ZDYnb/TEC_Driver/hardware/interview.kicad_pcb

## KiCad design Schematic/LaserTag.kicad_sch

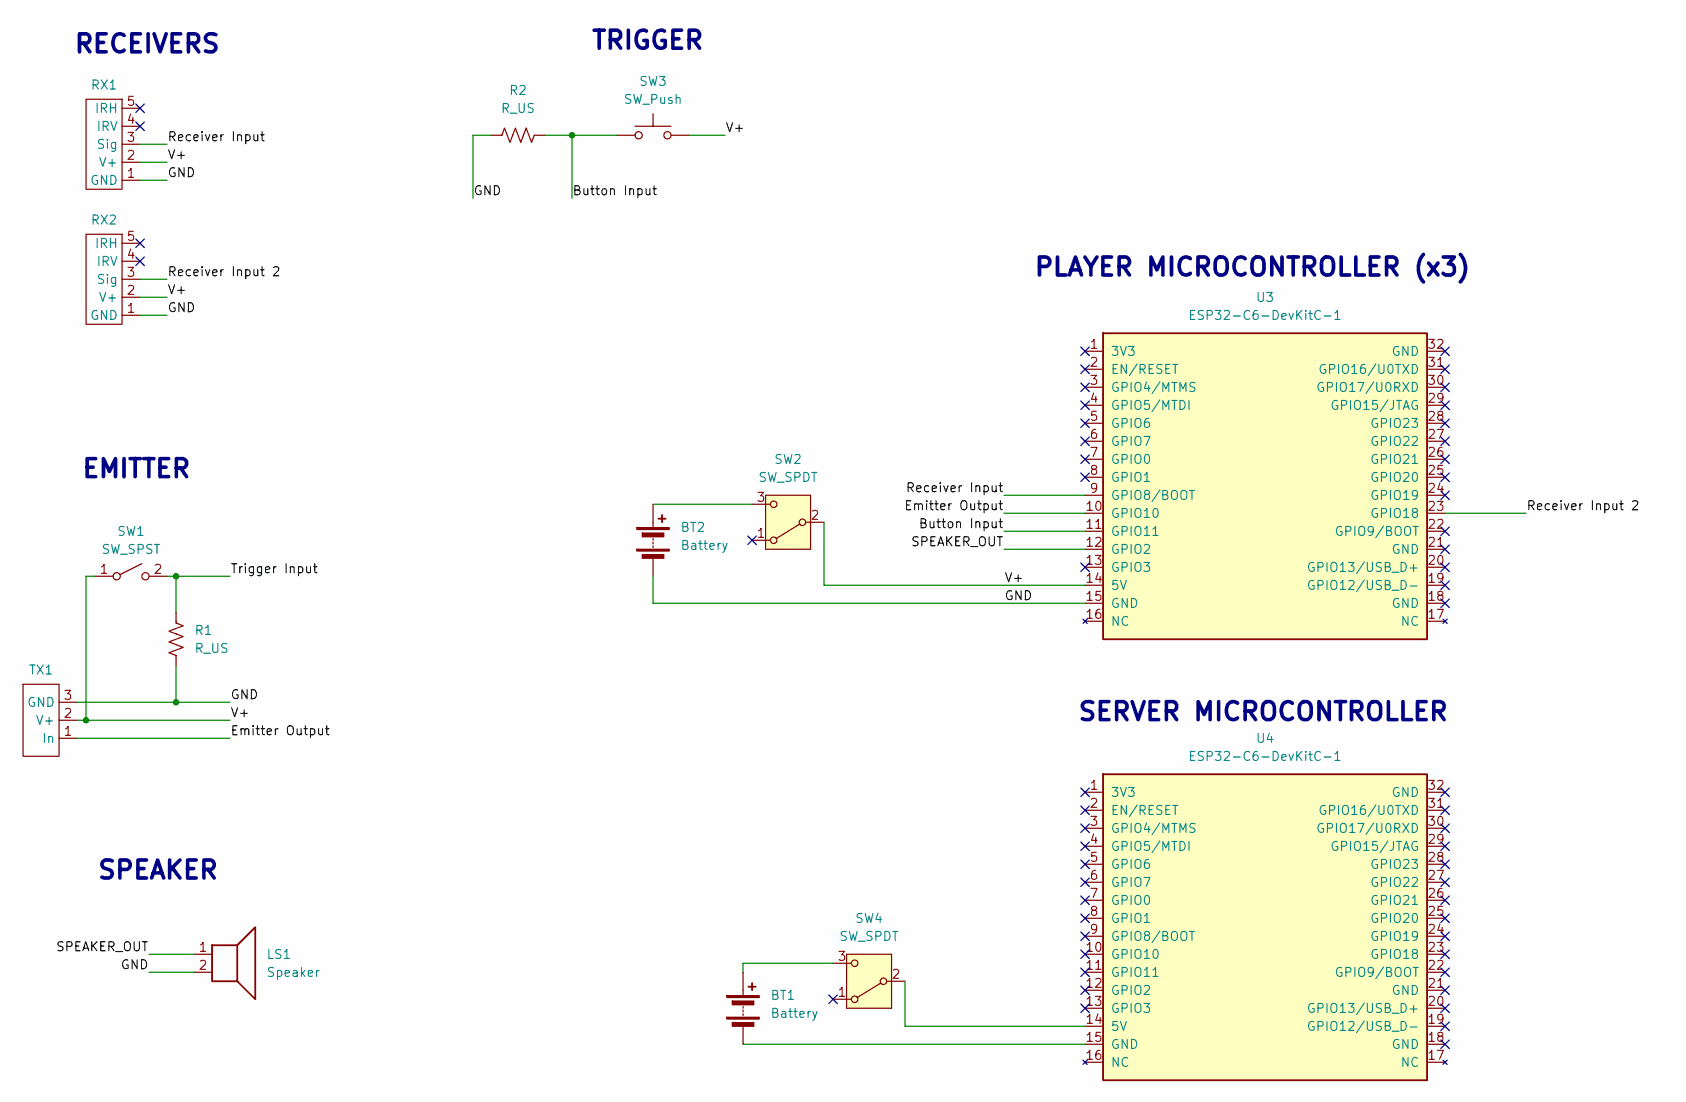
[picture p4: schematic LaserTag.kicad_sch]

Parts:
BT1, BT2: Battery
LS1: Speaker
R1, R2: R_US
RX1, RX2: (no value)
SW1: SW_SPST
SW2, SW4: SW_SPDT
SW3: SW_Push
TX1: (no value)
U3, U4: ESP32-C6-DevKitC-1

Connections:
Button Input: R2.2, SW3.1, U3.11 (GPIO11)
Emitter Output: TX1.1 (In), U3.10 (GPIO10)
GND: BT2.2 (-), LS1.2, R1.2, R2.1, RX1.1 (GND), RX2.1 (GND), TX1.3 (GND), U3.15 (GND)
unnamed: BT1.1 (+), SW4.3 (C)
unnamed: BT1.2 (-), U4.15 (GND)
unnamed: BT2.1 (+), SW2.3 (C)
unnamed: SW4.2 (B), U4.14 (5V)
Receiver Input: RX1.3 (Sig), U3.9 (GPIO8/BOOT)
Receiver Input 2: RX2.3 (Sig), U3.23 (GPIO18)
SPEAKER_OUT: LS1.1, U3.12 (GPIO2)
Trigger Input: R1.1, SW1.2 (B)
V+: RX1.2 (V+), RX2.2 (V+), SW1.1 (A), SW2.2 (B), SW3.2, TX1.2 (V+), U3.14 (5V)

Notes on the sheet:
SPEAKER
RECEIVERS
EMITTER
TRIGGER
PLAYER MICROCONTROLLER (x3)
SERVER MICROCONTROLLER
